hw-tinkerers/TR-60/3d-models/C_0805.STEP

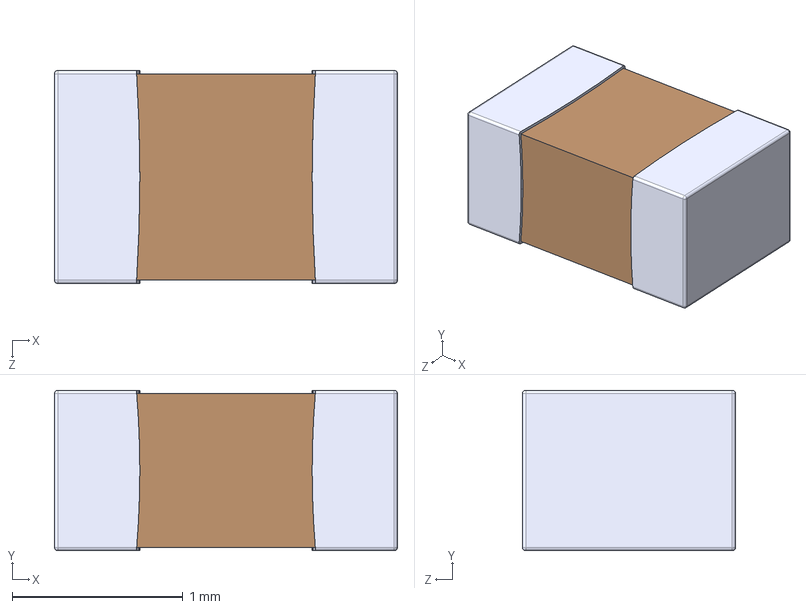
[picture p20: CAD file, 2023-08-22]
3d-models/C_0805.STEP
2.01 x 0.94 x 1.25 mm
