hw-tinkerers/TR-60/3d-models/JST-4pin.STEP

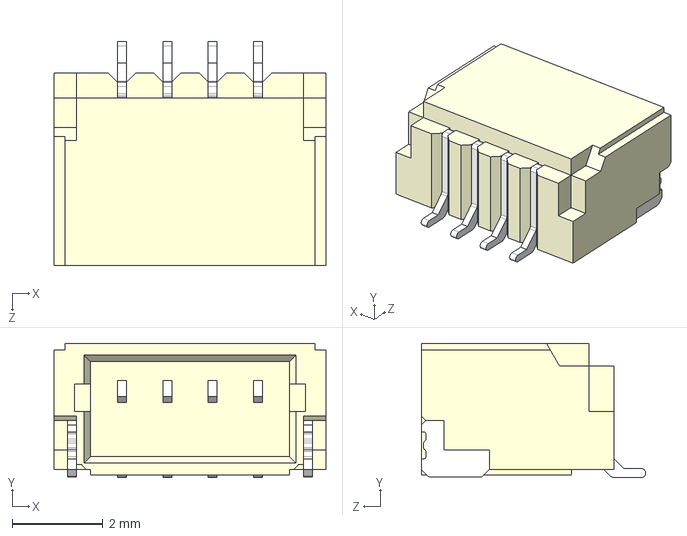
[picture p21: CAD file, 2023-08-22]
3d-models/JST-4pin.STEP
6.00 x 2.96 x 4.95 mm
