hw-tinkerers/TR-60/3d-models/C_0603.STEP

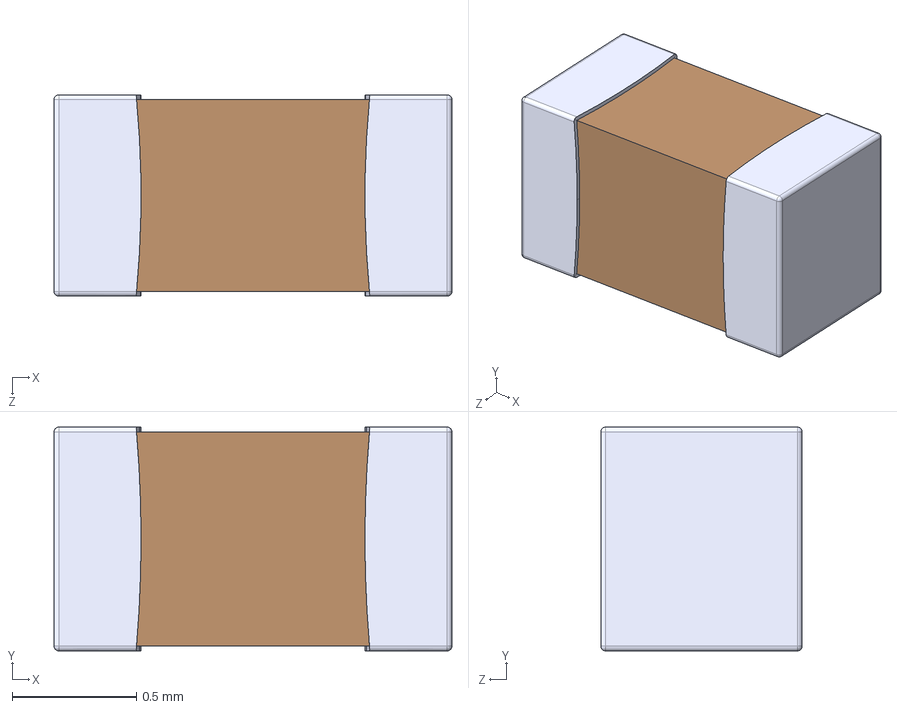
[picture p22: CAD file, 2023-08-22]
3d-models/C_0603.STEP
1.60 x 0.9 x 0.81 mm
