hw-tinkerers/TR-60/3d-models/LED_0603.STEP

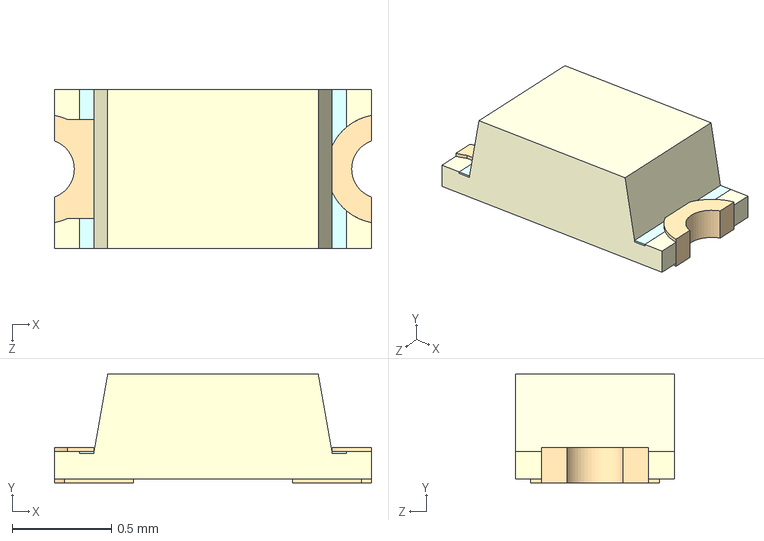
[picture p23: CAD file, 2023-08-22]
3d-models/LED_0603.STEP
1.60 x 0.55 x 0.8 mm
